robyale/DrinkBot/pumps.py

# Configuration of pumps
pumps = [
    {
        "name": "Pump 1",
        "pin": 1,
        "value": "tequila"
    },
    {
        "name": "Pump 2",
        "pin": 15,
        "value": "vodka"
    },
    {
        "name": "Pump 3",
        "pin": 2,
        "value": "tsec"
    },
    {
        "name": "Pump 4",
        "pin": 3,
        "value": "lime"
    }
]
