robyale/DrinkBot/drinks.py

# Drink list
drinkList = [
    {
        "name": "Margarita",
        "ingredients": {
            "lime": 20,
            "tequila": 20,
            "tsec": 10
        }
    },
    {
        "name": "Kamikaze",
        "ingredients": {
            "lime": 1,
            "vodka": 1,
            "tsec": 0.75
        }
    },
    {
        "name": "A Rough Day",
        "ingredients": {
            "water": 3
        }
    },
    {
        "name": "drink1",
        "ingredients": {
            "tequila": 3
        }
    },
    {
        "name": "drink2",
        "ingredients": {
            "tequila": 3
        }
    },
    {
        "name": "drink3",
        "ingredients": {
            "water": 3
        }
    },
    {
        "name": "drink4",
        "ingredients": {
            "tequila": 3
        }
    },
    {
        "name": "drink5",
        "ingredients": {
            "tequila": 3
        }
    }
]

ingredients = [
    {
        "name": "Tequila",
        "value": "tequila",
        "ingredients": {
            "tequila": 1
        }
    },
    {
        "name": "Vodka",
        "value": "vodka",
        "ingredients": {
            "vodka": 1
        }
    },
    {
        "name": "Triple Sec",
        "value": "tsec",
        "ingredients": {
            "tsec": 1
        }
    },
    {
        "name": "Lime Juice",
        "value": "lime",
        "ingredients": {
            "lime": 1
        }
    }
]
